graemedench/quadify_empowered/FM4 Button Print Pack/Individual STL Files/Play_Mode_-_Raised_0.2mm_Body.stl

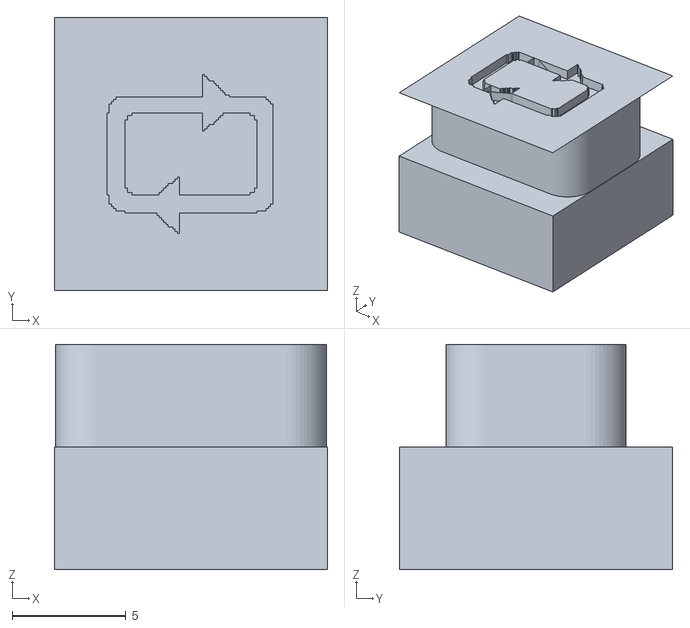
[picture p17: CAD file, 2026-09-27]
FM4 Button Print Pack/Individual STL Files/Play_Mode_-_Raised_0.2mm_Body.stl
12.0 x 12.0 x 9.90
