graemedench/quadify_empowered/FM4 Button Print Pack/Resin - Single Colour Raised 1mm/Save_-_Resin_Single_Colour_Raised_1mm.stl

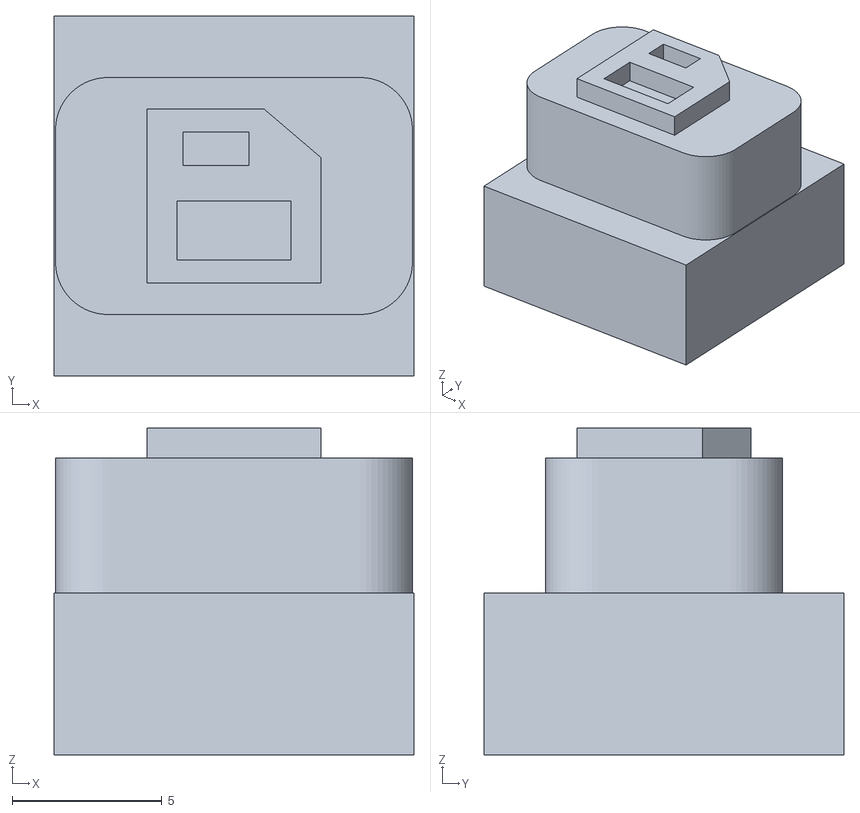
[picture p18: CAD file, 2026-09-27]
FM4 Button Print Pack/Resin - Single Colour Raised 1mm/Save_-_Resin_Single_Colour_Raised_1mm.stl
12.0 x 12.0 x 10.9
