graemedench/quadify_empowered/FM4 Button Print Pack/Individual STL Files/Skip_back_-_Raised_0.2mm_White.stl

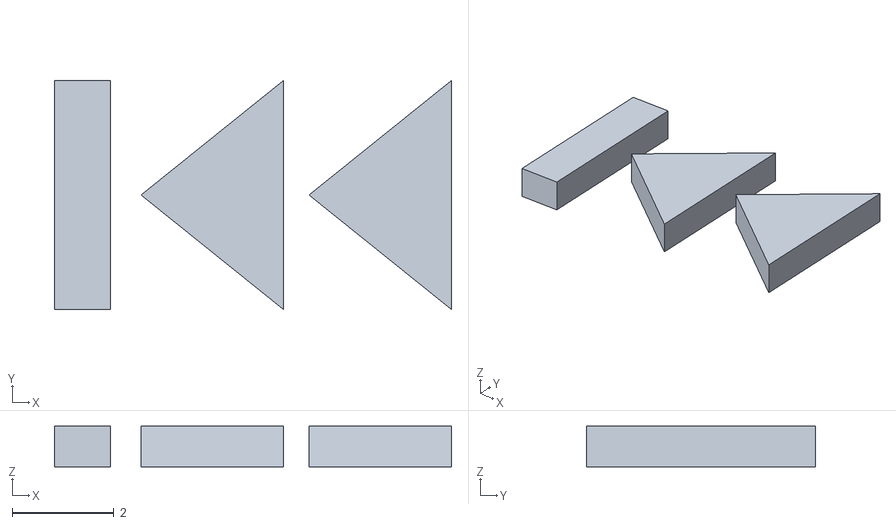
[picture p19: CAD file, 2026-09-27]
FM4 Button Print Pack/Individual STL Files/Skip_back_-_Raised_0.2mm_White.stl
7.80 x 4.50 x 0.8
