graemedench/quadify_empowered/FM4 Button Print Pack/Individual STL Files/Play_Pause_-_Flush_White.stl

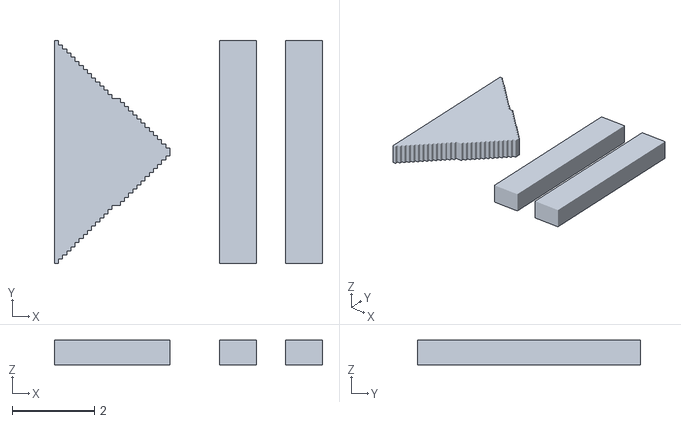
[picture p21: CAD file, 2026-09-27]
FM4 Button Print Pack/Individual STL Files/Play_Pause_-_Flush_White.stl
6.50 x 5.40 x 0.6
