graemedench/quadify_empowered/FM4 Button Print Pack/Individual STL Files/Play_Mode_-_Raised_0.2mm_White.stl

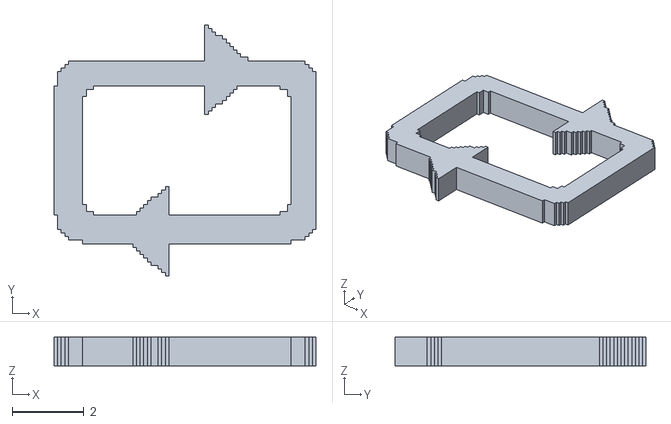
[picture p24: CAD file, 2026-09-27]
FM4 Button Print Pack/Individual STL Files/Play_Mode_-_Raised_0.2mm_White.stl
7.30 x 7.00 x 0.8
