graemedench/quadify_empowered/FM4 Button Print Pack/Individual STL Files/Play_-_Flush_White.stl

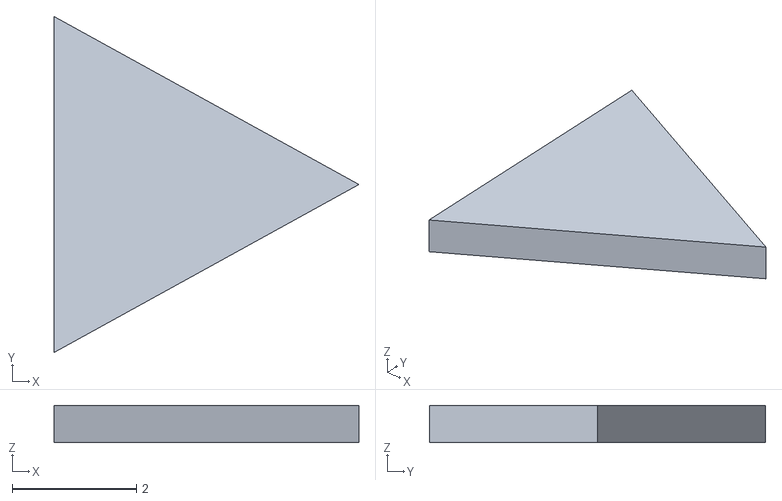
[picture p27: CAD file, 2026-09-27]
FM4 Button Print Pack/Individual STL Files/Play_-_Flush_White.stl
4.90 x 5.40 x 0.6
