graemedench/quadify_empowered/FM4 Button Print Pack/Individual STL Files/Save_-_Raised_0.2mm_White.stl

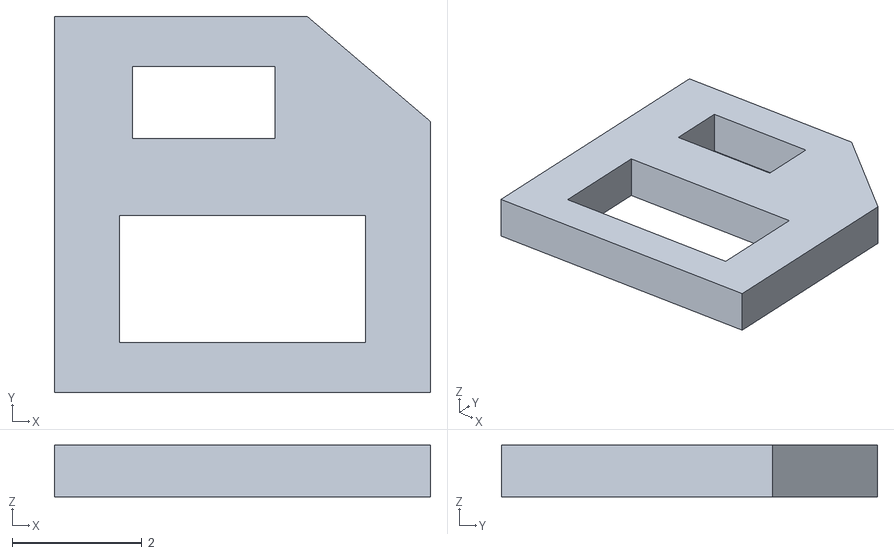
[picture p28: CAD file, 2026-09-27]
FM4 Button Print Pack/Individual STL Files/Save_-_Raised_0.2mm_White.stl
5.80 x 5.80 x 0.8
