graemedench/quadify_empowered/FM4 Button Print Pack/Individual STL Files/Pause_-_Flush_White.stl

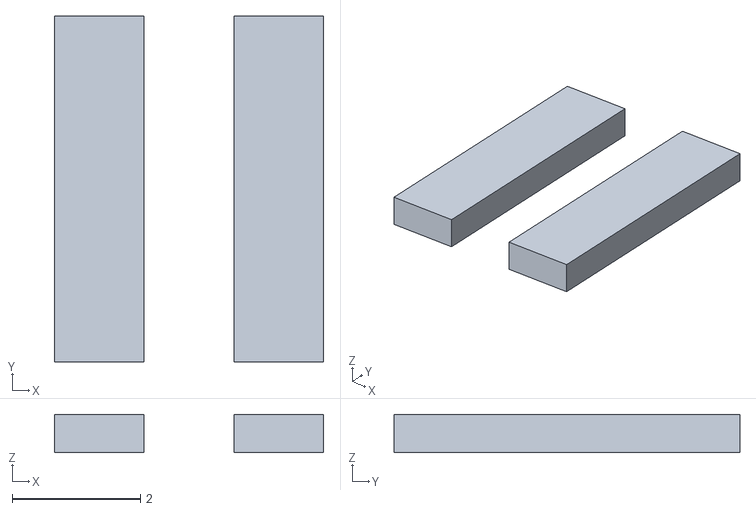
[picture p29: CAD file, 2026-09-27]
FM4 Button Print Pack/Individual STL Files/Pause_-_Flush_White.stl
4.20 x 5.40 x 0.6
