graemedench/quadify_empowered/FM4 Button Print Pack/Individual STL Files/BBC_4_-_Raised_0.2mm_White.stl

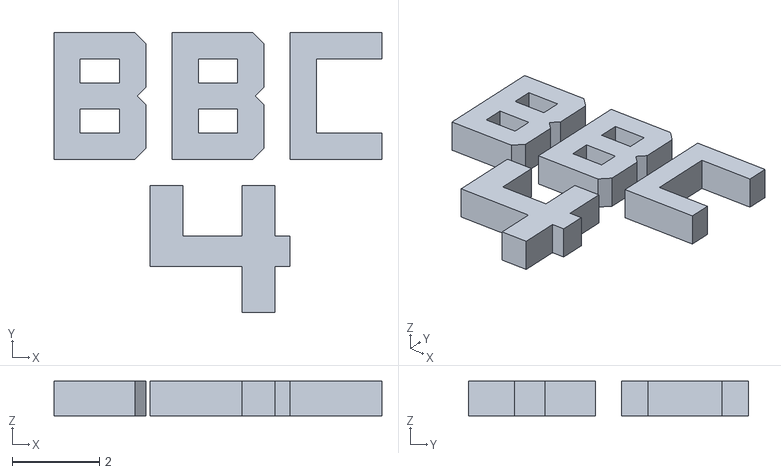
[picture p30: CAD file, 2026-09-27]
FM4 Button Print Pack/Individual STL Files/BBC_4_-_Raised_0.2mm_White.stl
7.50 x 6.40 x 0.8
