graemedench/quadify_empowered/FM4 Button Print Pack/Individual STL Files/Play_Pause_-_Raised_0.2mm_White_Overlay.stl

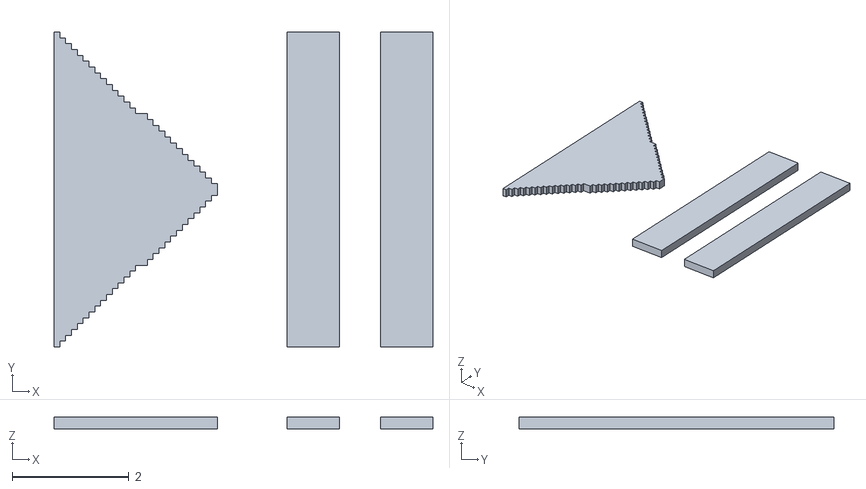
[picture p36: CAD file, 2026-09-27]
FM4 Button Print Pack/Individual STL Files/Play_Pause_-_Raised_0.2mm_White_Overlay.stl
6.50 x 5.40 x 0.2
