graemedench/quadify_empowered/FM4 Button Print Pack/Individual STL Files/Pause_-_Raised_0.2mm_White.stl

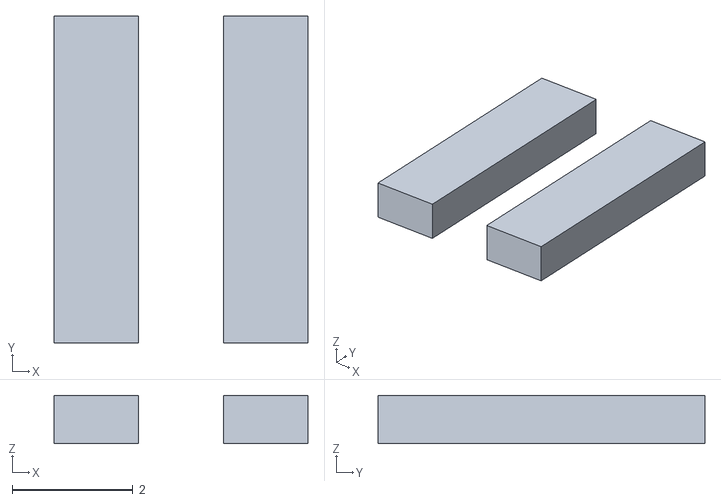
[picture p37: CAD file, 2026-09-27]
FM4 Button Print Pack/Individual STL Files/Pause_-_Raised_0.2mm_White.stl
4.20 x 5.40 x 0.8
