graemedench/quadify_empowered/FM4 Button Print Pack/Individual STL Files/TIDAL_-_Raised_0.2mm_White.stl

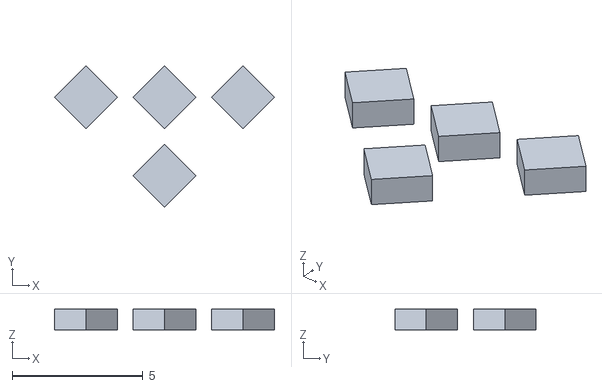
[picture p39: CAD file, 2026-09-27]
FM4 Button Print Pack/Individual STL Files/TIDAL_-_Raised_0.2mm_White.stl
8.40 x 5.40 x 0.8
